KosugiSubaru/kosugi_CPU0626/CPU/rtl/memory/imem/imem.v

module imem (
    input  wire         clk,
    input  wire [15:0]  i_addr,
    output wire [15:0]  o_instr
    );

    //命令メモリ本体
    reg [15:0] instmem [16383:0];//[32767:0];
    reg [15:0] i;

    // // バイトアドレッシング対応
    // wire [7:0] addr; 
    // assign addr = {i_addr[7:0]}; // 下位1ビットを無視

    wire [13:0] addr_extract;
    assign addr_extract = i_addr[13:0]; // 下位14ビット
    
    //非同期読み出し
    // assign o_instr = instmem[addr_extract];

    //同期読み出し
    assign o_instr = i;
    always@ (posedge clk) begin
        i <= instmem[addr_extract];
    end

    //初期化
    initial begin
        $readmemb("rtl/memory/imem/machine_code_bin.dat", instmem);
    end

    
endmodule
