KosugiSubaru/kosugi_CPU0626/CPU/rtl/cpu/alu/rtl/alu_full_adder_1bit.v

module alu_full_adder_1bit (
    input  wire i_a,
    input  wire i_b,
    input  wire i_cin,
    output wire o_sum,
    output wire o_cout
);

    // 1ビット全加算器の論理式
    // 回路図上でゲートの組み合わせとして視覚化される
    assign o_sum  = i_a ^ i_b ^ i_cin;
    assign o_cout = (i_a & i_b) | (i_b & i_cin) | (i_cin & i_a);

endmodule
